timberlupus/borneo/assets/blc05mk3-sch.png

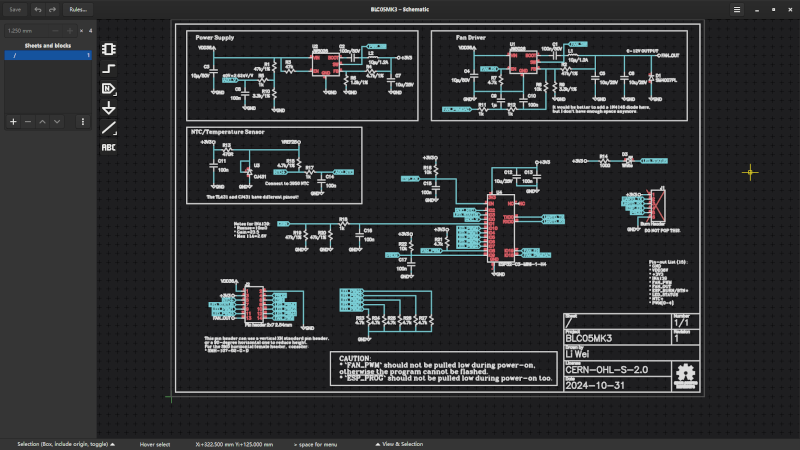
assets/blc05mk3-sch.png
