timberlupus/borneo/assets/blc06mk1-shot1.jpg

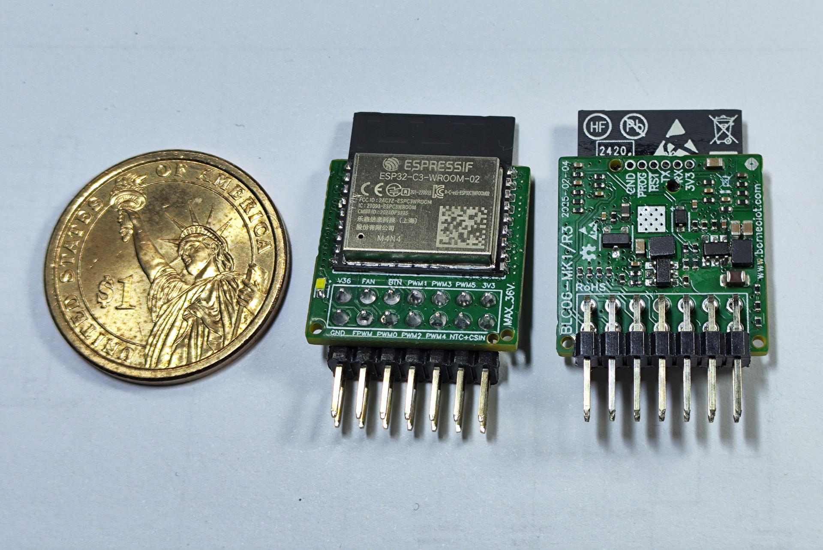
assets/blc06mk1-shot1.jpg
