timberlupus/borneo/hw/blb0657f/pool/3d_models/cache/6d752bc3-29b3-45df-8cf2-1e3aacefbcc6/3d_models/passive/resistor/R_0805_2012Metric.step

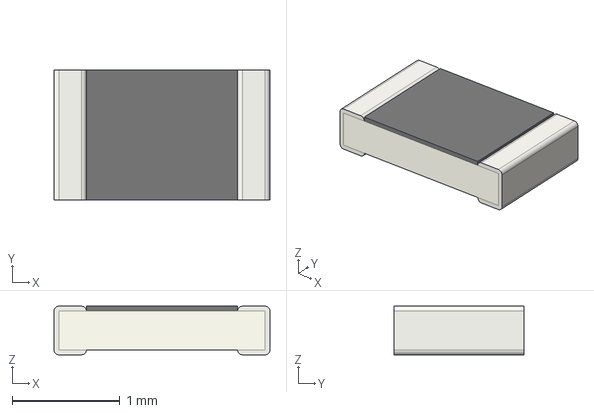
[picture p25: CAD file, 2025-01-13]
hw/blb0657f/pool/3d_models/cache/6d752bc3-29b3-45df-8cf2-1e3aacefbcc6/3d_models/passive/resistor/R_0805_2012Metric.step
2.00 x 1.20 x 0.45 mm
