timberlupus/borneo/hw/blb0657f/pool/3d_models/cache/8eeaf956-e4a0-4db5-95bb-b90e600e8069/3d_models/connector/b2w/2.54mm/2510_4p_smd_horizontal.step

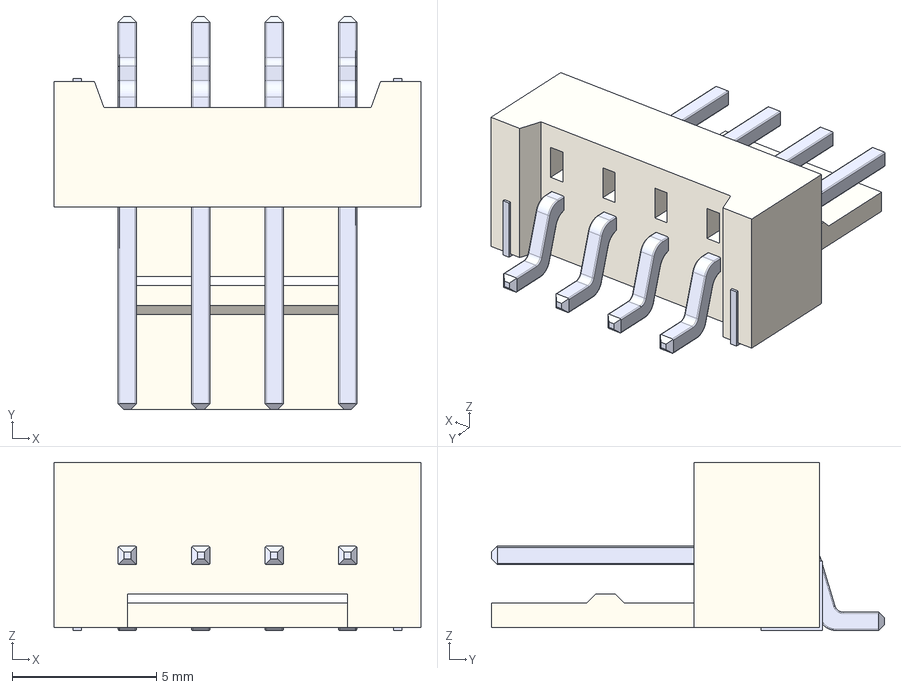
[picture p26: CAD file, 2025-01-13]
hw/blb0657f/pool/3d_models/cache/8eeaf956-e4a0-4db5-95bb-b90e600e8069/3d_models/connector/b2w/2.54mm/2510_4p_smd_horizontal.step
12.7 x 13.6 x 5.82 mm
