timberlupus/borneo/hw/blb0657f/pool/3d_models/cache/8eeaf956-e4a0-4db5-95bb-b90e600e8069/3d_models/connector/b2w/jst/2.00mm/S2B-PH-SM4-TB_LF__SN_.step

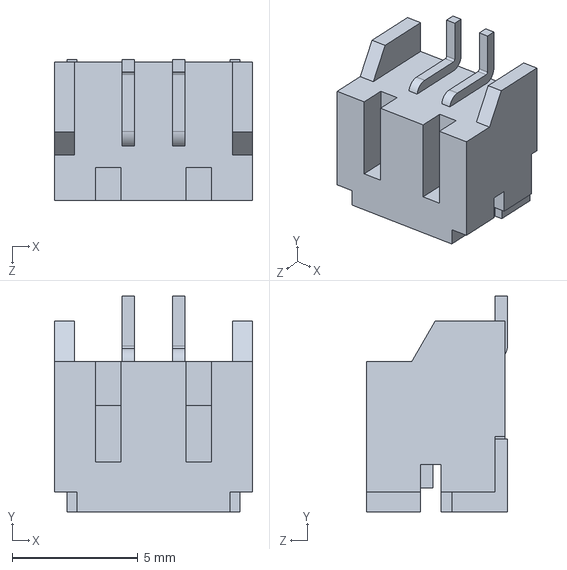
[picture p27: CAD file, 2025-02-11]
hw/blb0657f/pool/3d_models/cache/8eeaf956-e4a0-4db5-95bb-b90e600e8069/3d_models/connector/b2w/jst/2.00mm/S2B-PH-SM4-TB_LF__SN_.step
7.90 x 8.60 x 5.60 mm
