timberlupus/borneo/hw/blb0657f/pool/3d_models/cache/8eeaf956-e4a0-4db5-95bb-b90e600e8069/3d_models/connector/header/2.54mm/PinHeader_2x07_P2.54mm_Horizontal.step

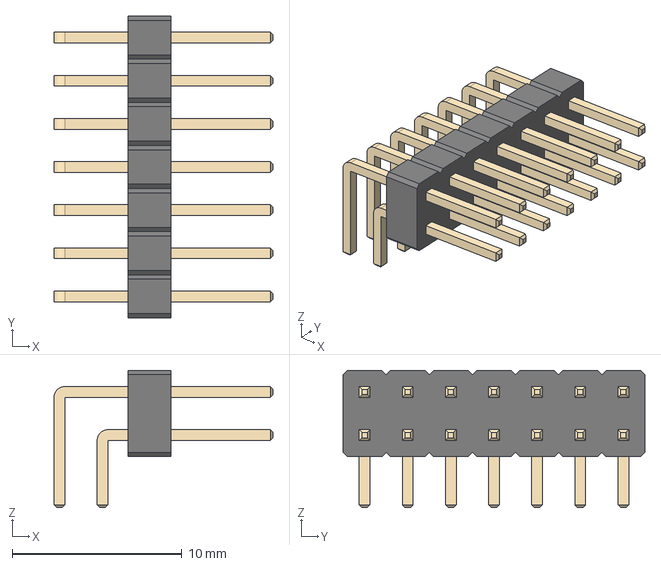
[picture p28: CAD file, 2025-01-13]
hw/blb0657f/pool/3d_models/cache/8eeaf956-e4a0-4db5-95bb-b90e600e8069/3d_models/connector/header/2.54mm/PinHeader_2x07_P2.54mm_Horizontal.step
12.9 x 17.8 x 8.08 mm
