timberlupus/borneo/hw/blb0657f/pool/3d_models/cache/8eeaf956-e4a0-4db5-95bb-b90e600e8069/3d_models/connector/header/samtec/2.54/SMH-107-02-G-D.stp

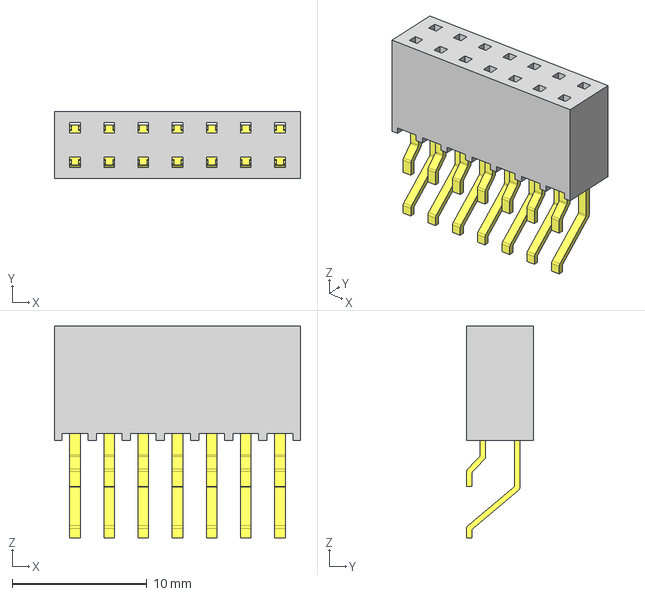
[picture p29: CAD file, 2025-01-13]
hw/blb0657f/pool/3d_models/cache/8eeaf956-e4a0-4db5-95bb-b90e600e8069/3d_models/connector/header/samtec/2.54/SMH-107-02-G-D.stp
18.3 x 4.95 x 15.7 mm
SMH-107-D_socket
C-08-03-07-D_SMH
