timberlupus/borneo/hw/blb0657f/pool/3d_models/cache/8eeaf956-e4a0-4db5-95bb-b90e600e8069/3d_models/connector/terminal-block/wago/2060-452_998-404.step

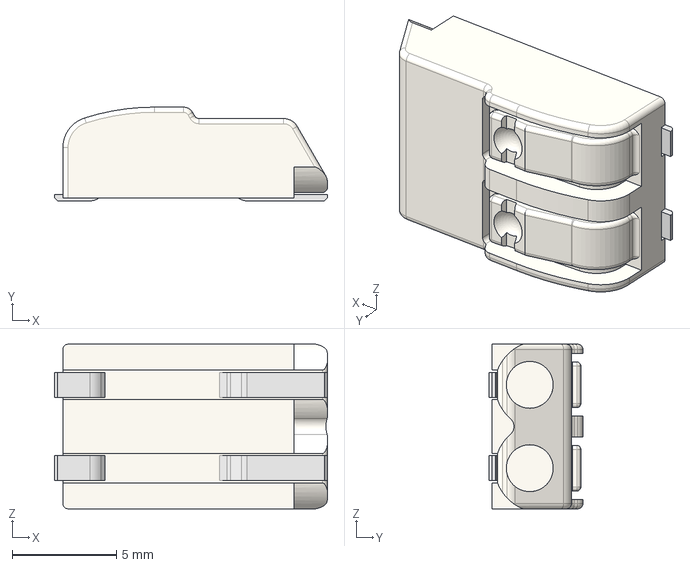
[picture p30: CAD file, 2025-02-11]
hw/blb0657f/pool/3d_models/cache/8eeaf956-e4a0-4db5-95bb-b90e600e8069/3d_models/connector/terminal-block/wago/2060-452_998-404.step
13.1 x 4.50 x 7.90 mm
