timberlupus/borneo/hw/blb0657f/pool/3d_models/cache/8eeaf956-e4a0-4db5-95bb-b90e600e8069/3d_models/ic/so/SOT-89-5.step

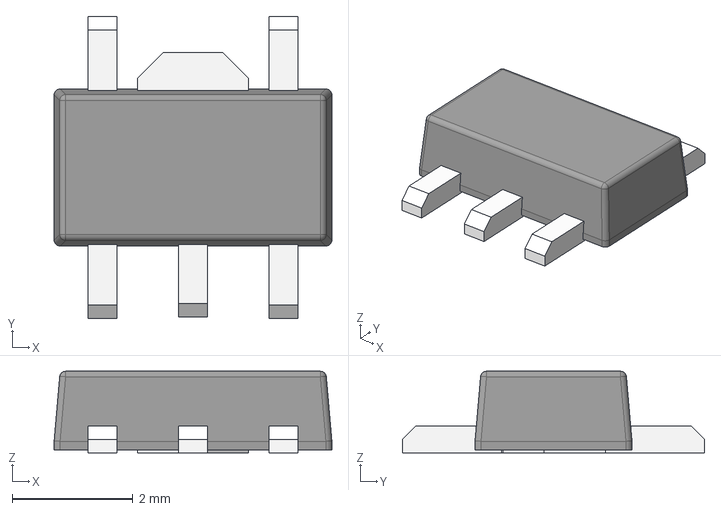
[picture p31: CAD file, 2025-02-04]
hw/blb0657f/pool/3d_models/cache/8eeaf956-e4a0-4db5-95bb-b90e600e8069/3d_models/ic/so/SOT-89-5.step
4.60 x 5.00 x 1.35 mm
