timberlupus/borneo/hw/blb0657f/pool/3d_models/cache/8eeaf956-e4a0-4db5-95bb-b90e600e8069/3d_models/module/bst/bld06-r1-3d-package.step

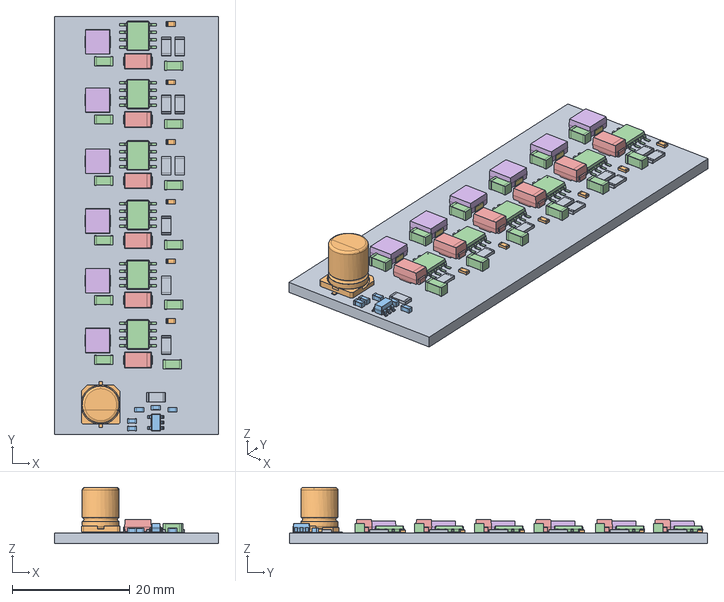
[picture p32: CAD file, 2025-02-08]
hw/blb0657f/pool/3d_models/cache/8eeaf956-e4a0-4db5-95bb-b90e600e8069/3d_models/module/bst/bld06-r1-3d-package.step
27.9 x 71.1 x 9.55 mm
