timberlupus/borneo/hw/blb0657f/pool/3d_models/cache/8eeaf956-e4a0-4db5-95bb-b90e600e8069/3d_models/opto/LED_SMDLED_1W_3W_R8-3DModel.step

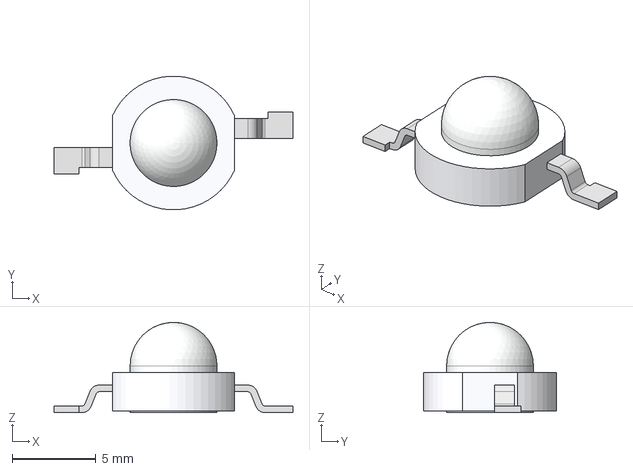
[picture p33: CAD file, 2025-01-13]
hw/blb0657f/pool/3d_models/cache/8eeaf956-e4a0-4db5-95bb-b90e600e8069/3d_models/opto/LED_SMDLED_1W_3W_R8-3DModel.step
14.3 x 7.99 x 5.40 mm
