timberlupus/borneo/hw/blb0657f/pool/3d_models/cache/8eeaf956-e4a0-4db5-95bb-b90e600e8069/3d_models/passive/capacitor/polarized/CP_Elec_6.3x7.7.step

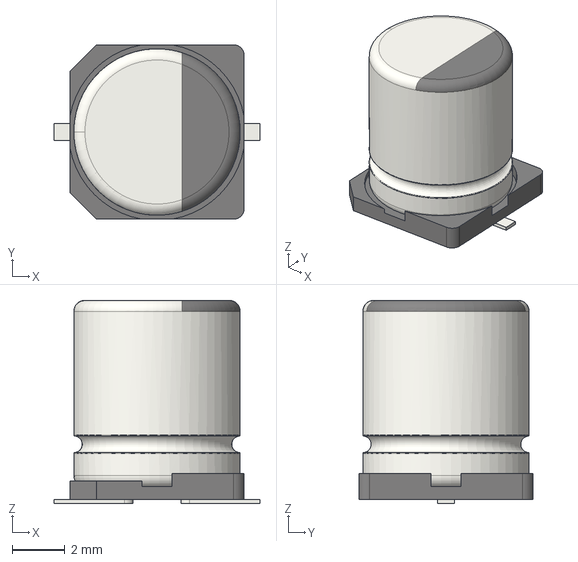
[picture p34: CAD file, 2025-01-13]
hw/blb0657f/pool/3d_models/cache/8eeaf956-e4a0-4db5-95bb-b90e600e8069/3d_models/passive/capacitor/polarized/CP_Elec_6.3x7.7.step
7.80 x 6.60 x 7.70 mm
