timberlupus/borneo/hw/blb0657f/pool/3d_models/cache/8eeaf956-e4a0-4db5-95bb-b90e600e8069/3d_models/passive/inductor/cjang/L_Changjiang_FNR4030S.step

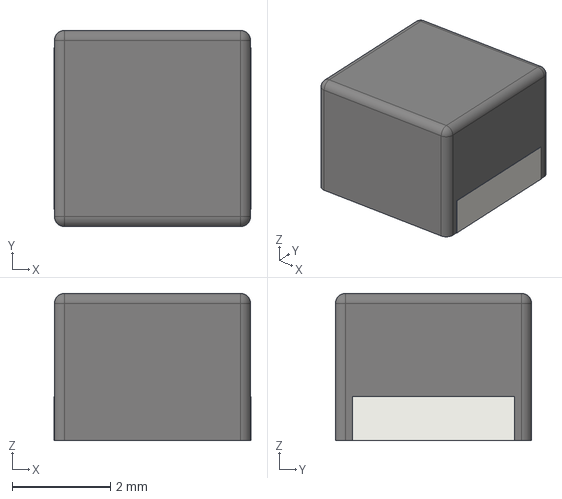
[picture p35: CAD file, 2025-02-04]
hw/blb0657f/pool/3d_models/cache/8eeaf956-e4a0-4db5-95bb-b90e600e8069/3d_models/passive/inductor/cjang/L_Changjiang_FNR4030S.step
4.02 x 4.00 x 3.00 mm
