timberlupus/borneo/hw/blb0657f/pool/3d_models/cache/8eeaf956-e4a0-4db5-95bb-b90e600e8069/3d_models/passive/inductor/tdk/L_TDK_SLF10145.step

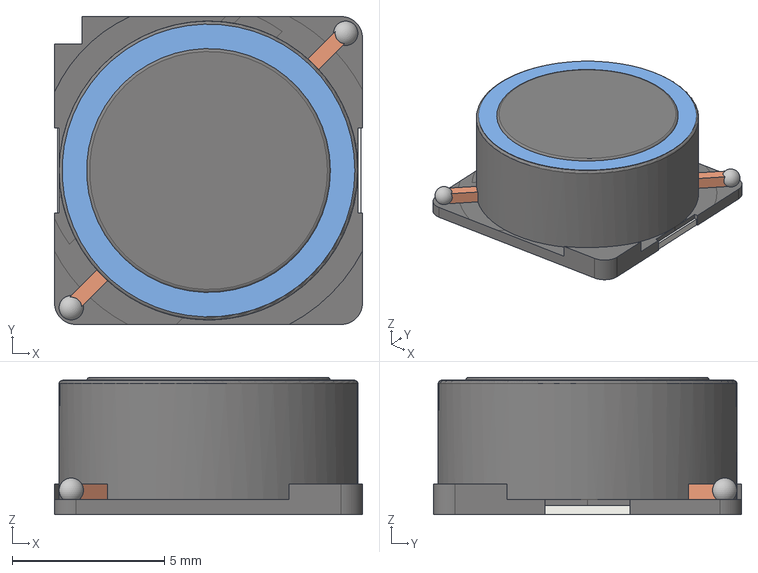
[picture p36: CAD file, 2025-01-13]
hw/blb0657f/pool/3d_models/cache/8eeaf956-e4a0-4db5-95bb-b90e600e8069/3d_models/passive/inductor/tdk/L_TDK_SLF10145.step
10.1 x 10.1 x 4.50 mm
