timberlupus/borneo/hw/blb0657f/pool/3d_models/cache/8eeaf956-e4a0-4db5-95bb-b90e600e8069/3d_models/passive/jump/smd/Jumper_0R0_10.2x1.5mm.step

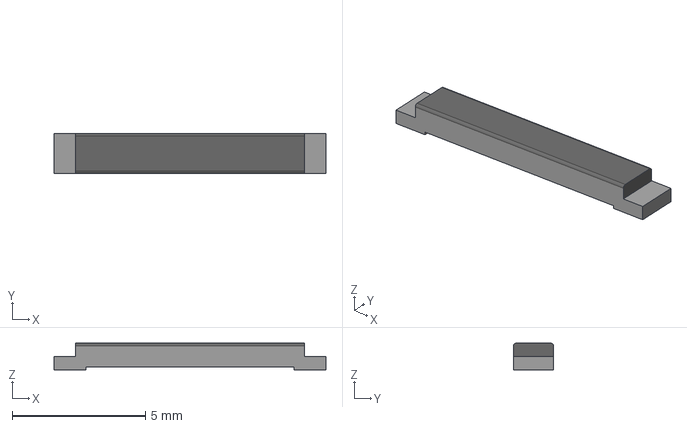
[picture p37: CAD file, 2025-02-08]
hw/blb0657f/pool/3d_models/cache/8eeaf956-e4a0-4db5-95bb-b90e600e8069/3d_models/passive/jump/smd/Jumper_0R0_10.2x1.5mm.step
10.2 x 1.50 x 1.00 mm
