timberlupus/borneo/hw/blb08103/pool/3d_models/cache/8eeaf956-e4a0-4db5-95bb-b90e600e8069/3d_models/connector/b2w/jst/2.50mm/S4B-XH-SM4-TB.STEP

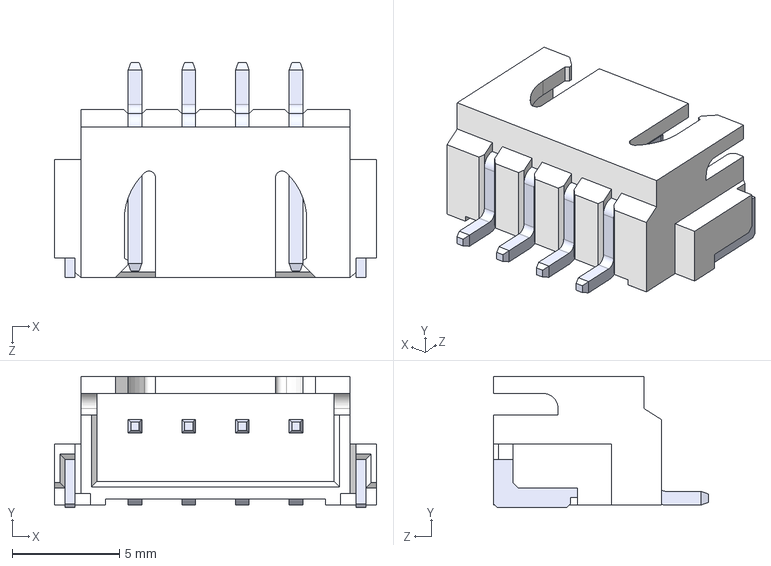
[picture p38: CAD file, 2025-01-13]
hw/blb08103/pool/3d_models/cache/8eeaf956-e4a0-4db5-95bb-b90e600e8069/3d_models/connector/b2w/jst/2.50mm/S4B-XH-SM4-TB.STEP
15.0 x 6.12 x 10.0 mm
SxB-XH-SM4-TB_4
pin^SxB-XH-SM4-TB Ass x 4
