timberlupus/borneo/hw/blb08103/pool/3d_models/cache/8eeaf956-e4a0-4db5-95bb-b90e600e8069/3d_models/ic/so/TSSOP-20_4.4x6.5mm_P0.65mm.step

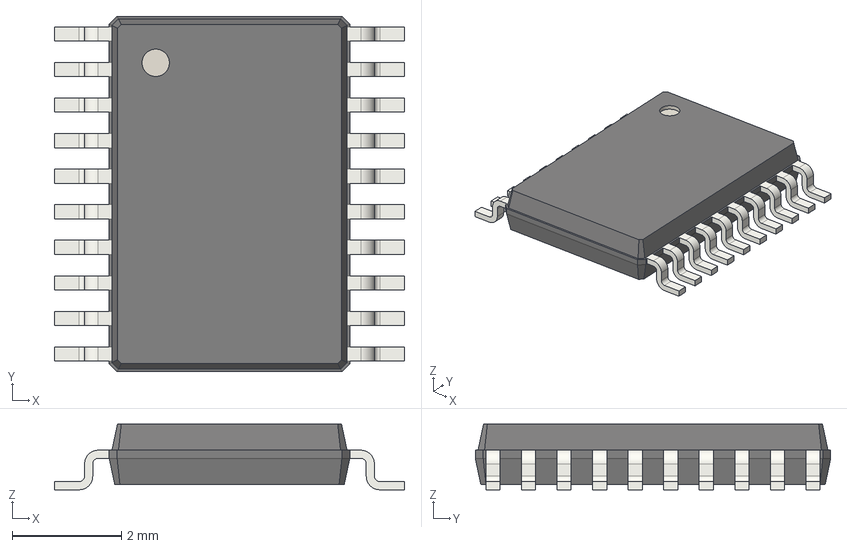
[picture p39: CAD file, 2025-01-13]
hw/blb08103/pool/3d_models/cache/8eeaf956-e4a0-4db5-95bb-b90e600e8069/3d_models/ic/so/TSSOP-20_4.4x6.5mm_P0.65mm.step
6.40 x 6.50 x 1.20 mm
