timberlupus/borneo/hw/blb08103/pool/3d_models/cache/8eeaf956-e4a0-4db5-95bb-b90e600e8069/3d_models/passive/fuse/Fuse_1210_3225Metric.step

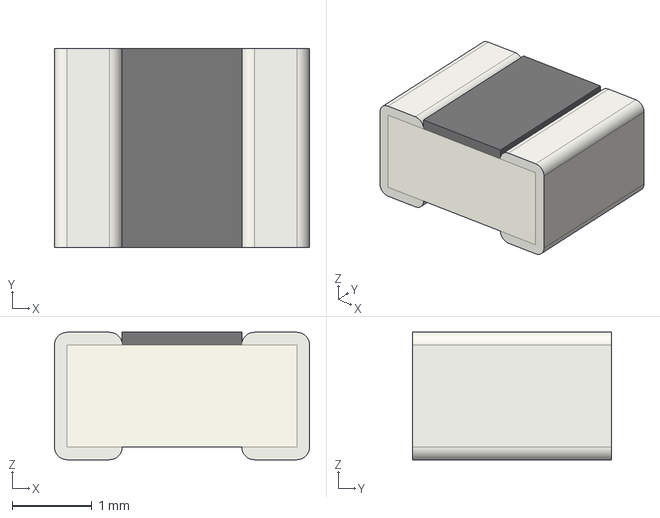
[picture p40: CAD file, 2025-01-13]
hw/blb08103/pool/3d_models/cache/8eeaf956-e4a0-4db5-95bb-b90e600e8069/3d_models/passive/fuse/Fuse_1210_3225Metric.step
3.20 x 2.50 x 1.60 mm
