timberlupus/borneo/hw/blc06/pool/3d_models/cache/6d752bc3-29b3-45df-8cf2-1e3aacefbcc6/3d_models/connector/header/2.54mm/PinHeader_2x08_P2.54mm_Vertical.step

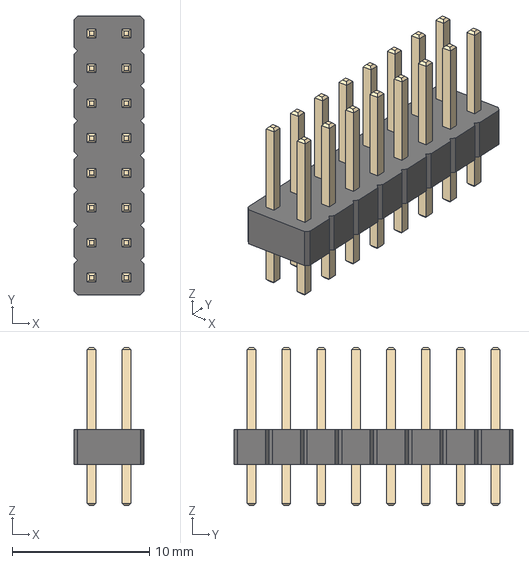
[picture p41: CAD file, 2025-02-01]
hw/blc06/pool/3d_models/cache/6d752bc3-29b3-45df-8cf2-1e3aacefbcc6/3d_models/connector/header/2.54mm/PinHeader_2x08_P2.54mm_Vertical.step
5.08 x 20.3 x 11.5 mm
