timberlupus/borneo/hw/blc06/pool/3d_models/cache/6d752bc3-29b3-45df-8cf2-1e3aacefbcc6/3d_models/diode/D_SOD-323.step

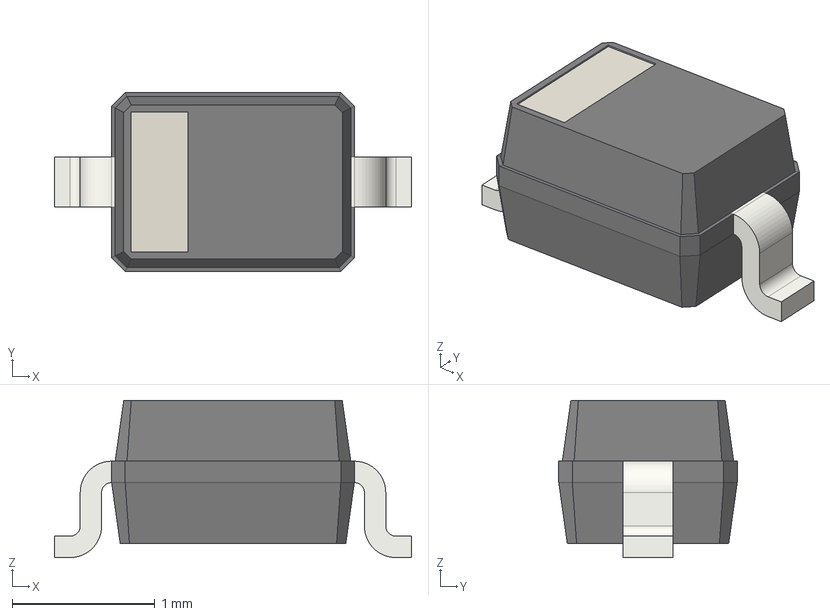
[picture p42: CAD file, 2025-01-13]
hw/blc06/pool/3d_models/cache/6d752bc3-29b3-45df-8cf2-1e3aacefbcc6/3d_models/diode/D_SOD-323.step
2.50 x 1.25 x 1.10 mm
