timberlupus/borneo/hw/blc06/pool/3d_models/cache/6d752bc3-29b3-45df-8cf2-1e3aacefbcc6/3d_models/passive/resistor/R_0402_1005Metric.step

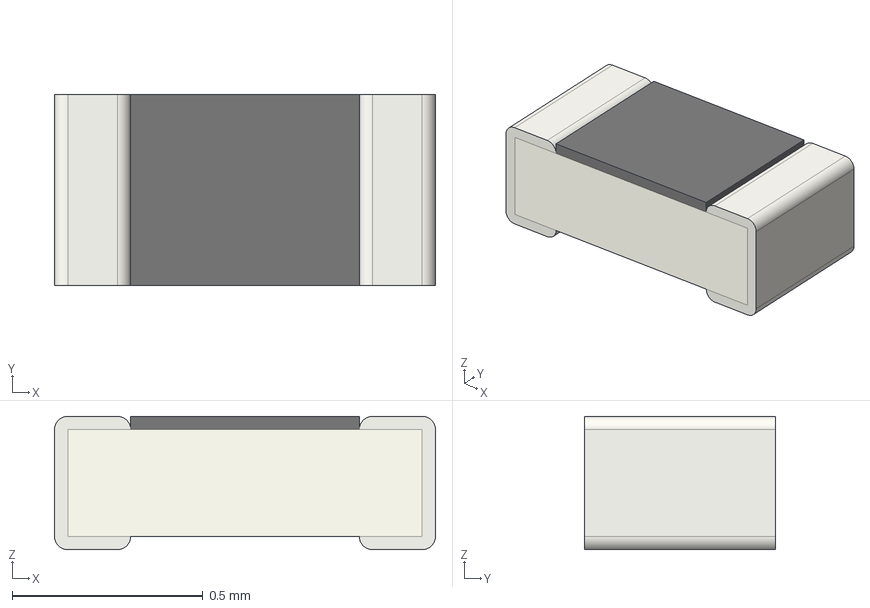
[picture p45: CAD file, 2025-01-13]
hw/blc06/pool/3d_models/cache/6d752bc3-29b3-45df-8cf2-1e3aacefbcc6/3d_models/passive/resistor/R_0402_1005Metric.step
1.00 x 0.5 x 0.35 mm
