timberlupus/borneo/hw/blc06/pool/3d_models/cache/8eeaf956-e4a0-4db5-95bb-b90e600e8069/3d_models/connector/header/1.27mm/PinHeader_1x06_P1.27mm_Vertical.step

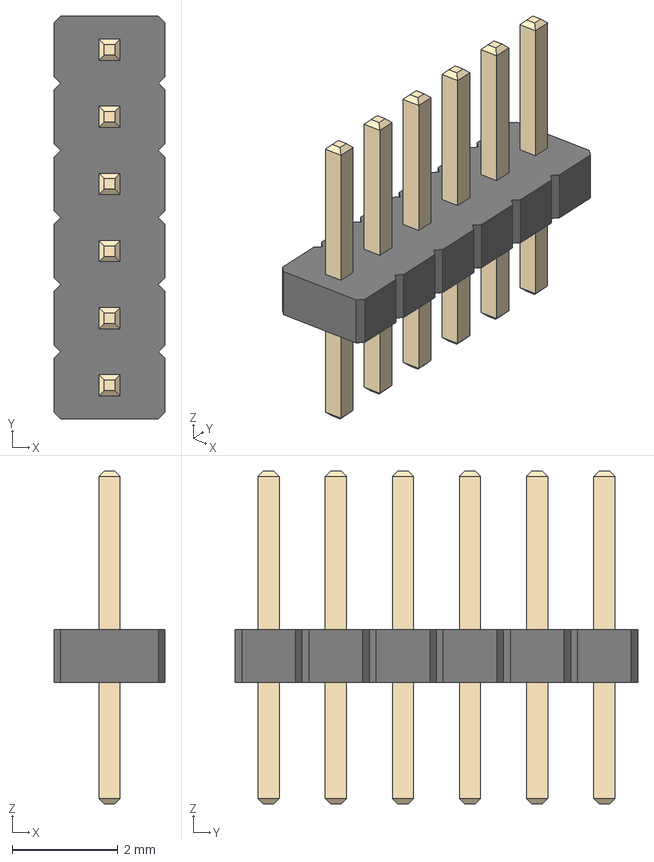
[picture p46: CAD file, 2025-01-13]
hw/blc06/pool/3d_models/cache/8eeaf956-e4a0-4db5-95bb-b90e600e8069/3d_models/connector/header/1.27mm/PinHeader_1x06_P1.27mm_Vertical.step
2.10 x 7.62 x 6.30 mm
