timberlupus/borneo/hw/blc06/pool/3d_models/cache/8eeaf956-e4a0-4db5-95bb-b90e600e8069/3d_models/ic/qfn/QFN-28-1EP_4x4mm_P0.4mm_EP2.4x2.4mm.step

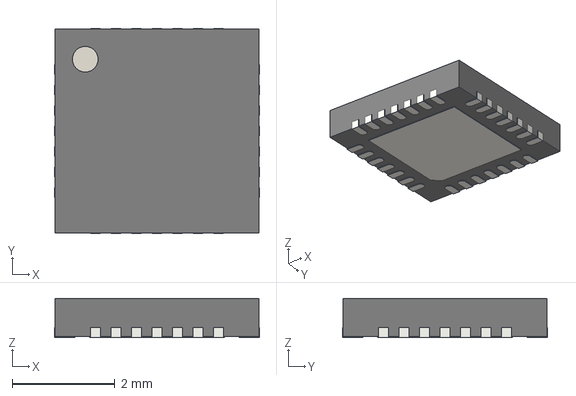
[picture p47: CAD file, 2025-01-13]
hw/blc06/pool/3d_models/cache/8eeaf956-e4a0-4db5-95bb-b90e600e8069/3d_models/ic/qfn/QFN-28-1EP_4x4mm_P0.4mm_EP2.4x2.4mm.step
4.00 x 4.00 x 0.77 mm
