timberlupus/borneo/hw/blc06/pool/3d_models/cache/8eeaf956-e4a0-4db5-95bb-b90e600e8069/3d_models/ic/so/SOT-23-6.step

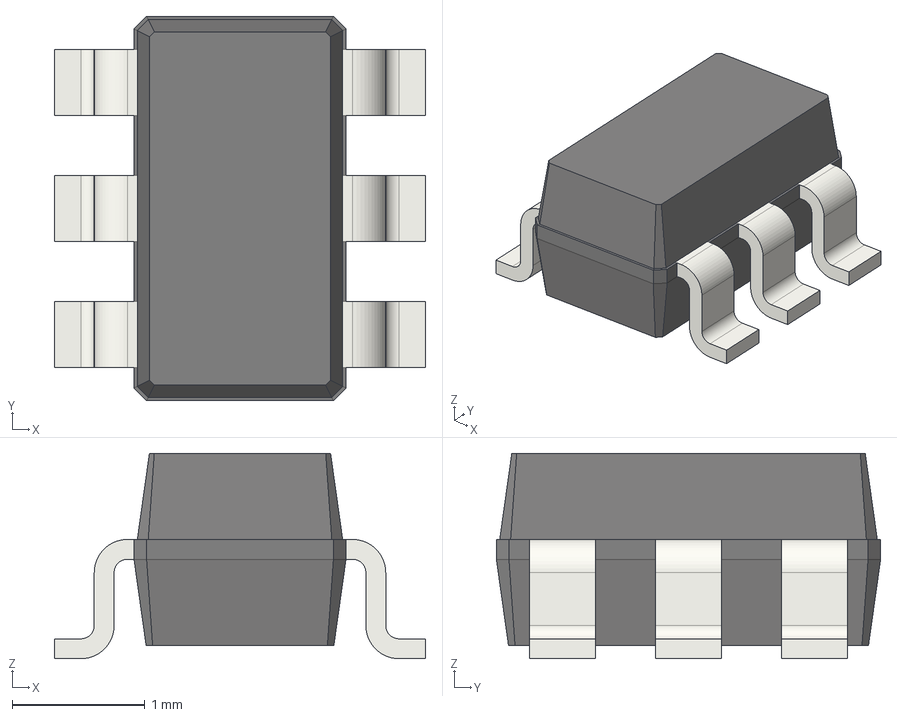
[picture p48: CAD file, 2025-01-13]
hw/blc06/pool/3d_models/cache/8eeaf956-e4a0-4db5-95bb-b90e600e8069/3d_models/ic/so/SOT-23-6.step
2.80 x 2.90 x 1.55 mm
