timberlupus/borneo/hw/blc06/pool/3d_models/cache/8eeaf956-e4a0-4db5-95bb-b90e600e8069/3d_models/ic/wson/WSON-8-1EP_2x2mm_P0.5mm_EP0.9x1.6mm.step

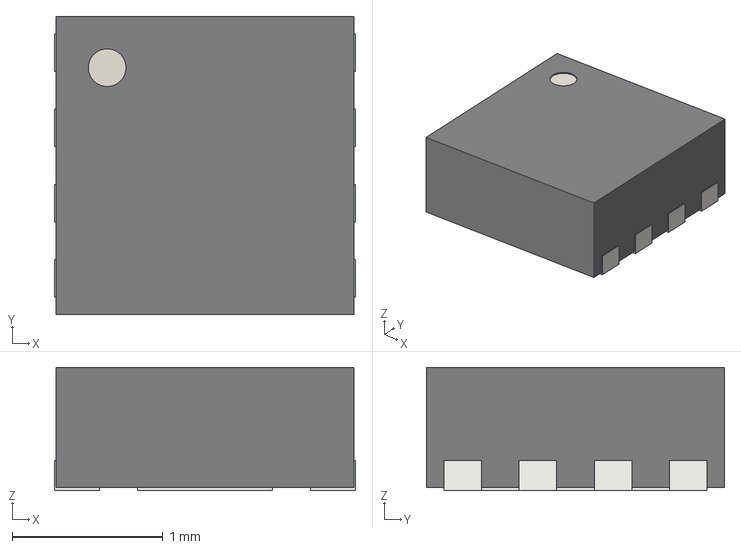
[picture p49: CAD file, 2025-02-01]
hw/blc06/pool/3d_models/cache/8eeaf956-e4a0-4db5-95bb-b90e600e8069/3d_models/ic/wson/WSON-8-1EP_2x2mm_P0.5mm_EP0.9x1.6mm.step
2.00 x 1.98 x 0.82 mm
