timberlupus/borneo/hw/blc06/pool/3d_models/cache/8eeaf956-e4a0-4db5-95bb-b90e600e8069/3d_models/module/rf/espressif/ESP32-C3-WROOM-02.stp

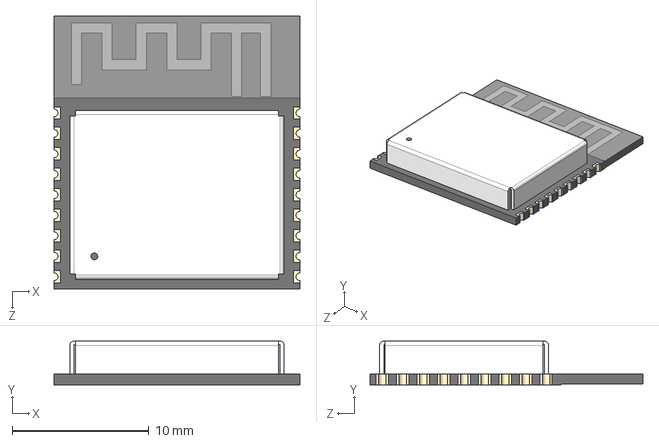
[picture p50: CAD file, 2025-03-12]
hw/blc06/pool/3d_models/cache/8eeaf956-e4a0-4db5-95bb-b90e600e8069/3d_models/module/rf/espressif/ESP32-C3-WROOM-02.stp
18.0 x 3.20 x 20.0 mm
