timberlupus/borneo/hw/blc06/pool/3d_models/cache/8eeaf956-e4a0-4db5-95bb-b90e600e8069/3d_models/opto/LED_0402_1005Metric.step

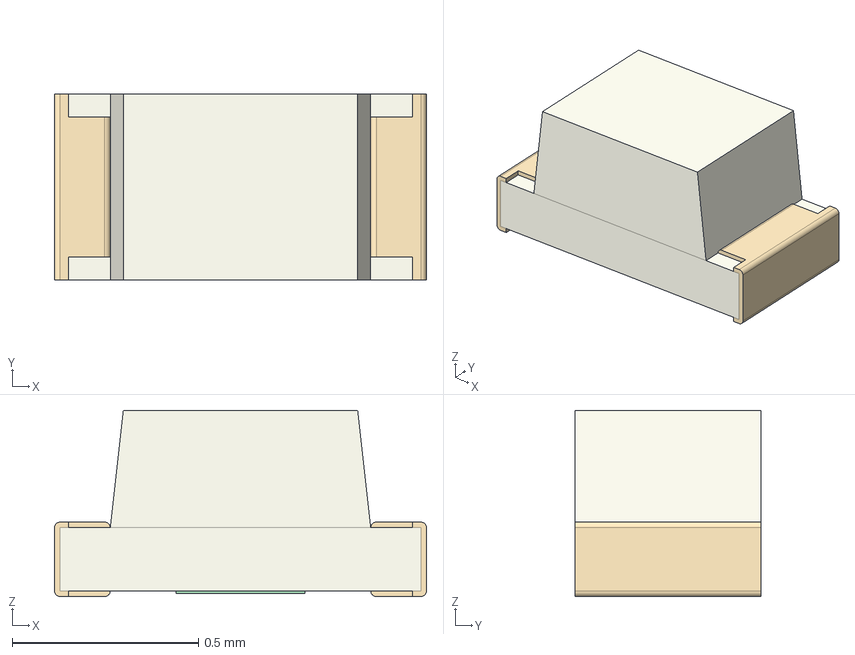
[picture p51: CAD file, 2025-02-17]
hw/blc06/pool/3d_models/cache/8eeaf956-e4a0-4db5-95bb-b90e600e8069/3d_models/opto/LED_0402_1005Metric.step
1.00 x 0.5 x 0.5 mm
