timberlupus/borneo/hw/blc06/pool/3d_models/cache/8eeaf956-e4a0-4db5-95bb-b90e600e8069/3d_models/passive/inductor/cjang/L_Changjiang_FNR3015S.step

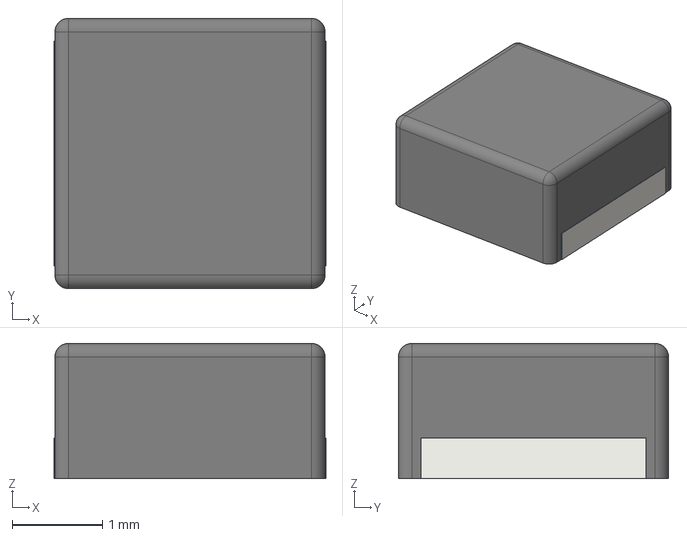
[picture p53: CAD file, 2025-01-13]
hw/blc06/pool/3d_models/cache/8eeaf956-e4a0-4db5-95bb-b90e600e8069/3d_models/passive/inductor/cjang/L_Changjiang_FNR3015S.step
3.02 x 3.00 x 1.50 mm
