timberlupus/borneo/hw/bld6f/pool/3d_models/cache/6d752bc3-29b3-45df-8cf2-1e3aacefbcc6/3d_models/passive/resistor/R_0603_1608Metric.step

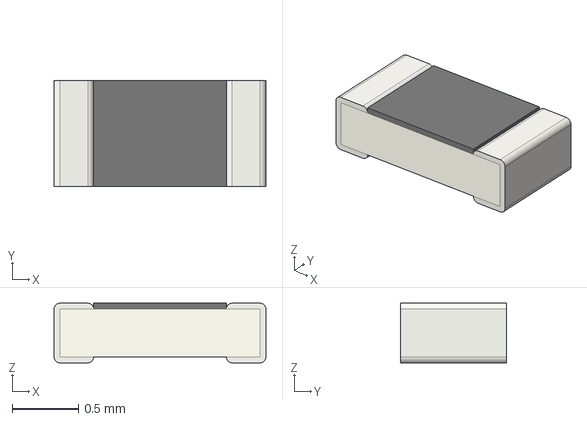
[picture p54: CAD file, 2025-01-13]
hw/bld6f/pool/3d_models/cache/6d752bc3-29b3-45df-8cf2-1e3aacefbcc6/3d_models/passive/resistor/R_0603_1608Metric.step
1.60 x 0.8 x 0.45 mm
