timberlupus/borneo/hw/bld6f/pool/3d_models/cache/8eeaf956-e4a0-4db5-95bb-b90e600e8069/3d_models/passive/inductor/sunlord/MWSA0402S.step

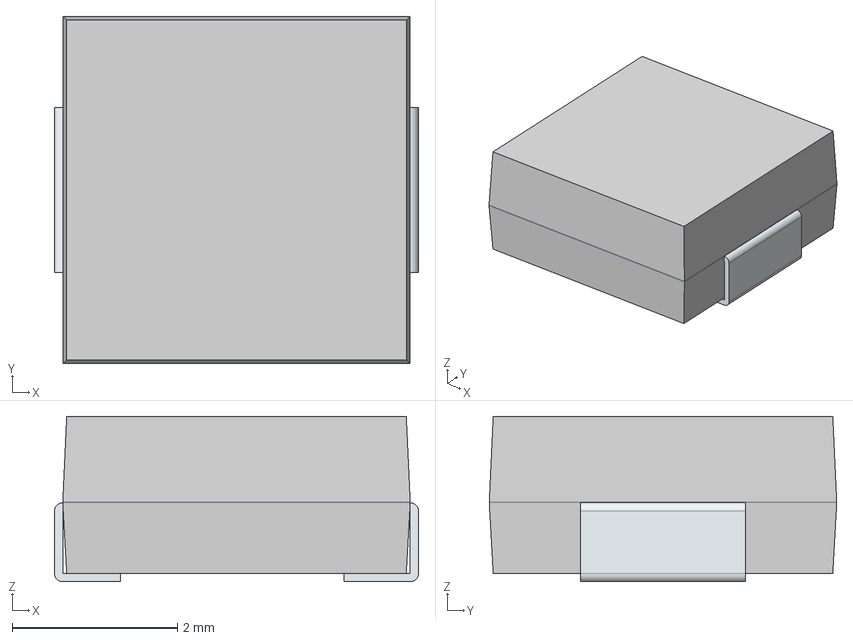
[picture p55: CAD file, 2025-02-08]
hw/bld6f/pool/3d_models/cache/8eeaf956-e4a0-4db5-95bb-b90e600e8069/3d_models/passive/inductor/sunlord/MWSA0402S.step
4.40 x 4.20 x 2.00 mm
FilletPin1
FilletPin2
