timberlupus/borneo/hw/bdb6mk1/pool/3d_models/cache/6d752bc3-29b3-45df-8cf2-1e3aacefbcc6/3d_models/ic/so/SOT-23.step

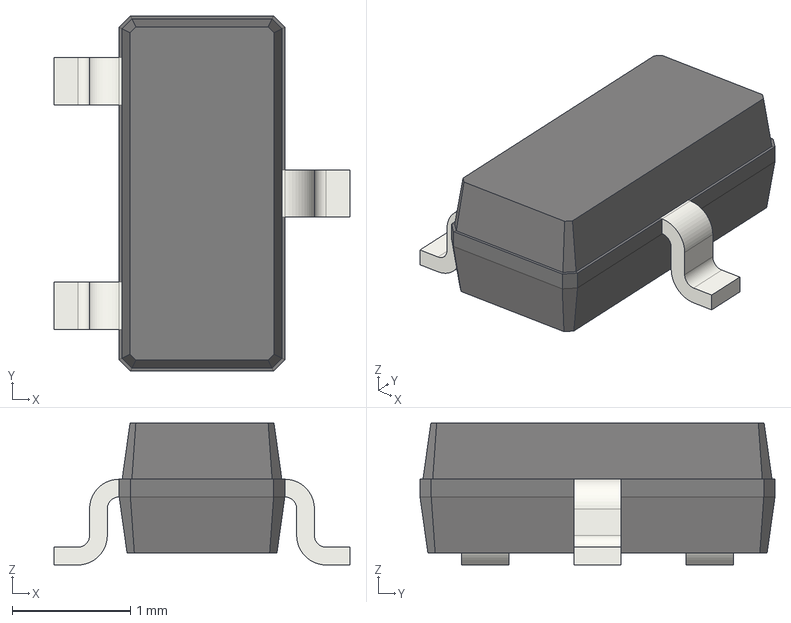
[picture p56: CAD file, 2025-01-13]
hw/bdb6mk1/pool/3d_models/cache/6d752bc3-29b3-45df-8cf2-1e3aacefbcc6/3d_models/ic/so/SOT-23.step
2.50 x 3.00 x 1.20 mm
