timberlupus/borneo/hw/bdb6mk1/pool/3d_models/cache/8eeaf956-e4a0-4db5-95bb-b90e600e8069/3d_models/module/rf/espressif/ESP32-C3-WROOM-02.STEP

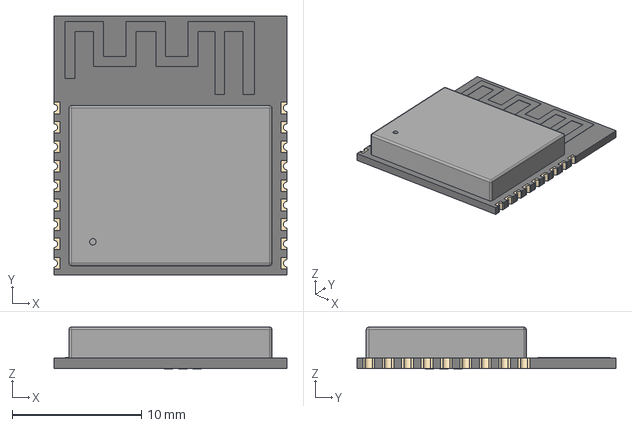
[picture p57: CAD file, 2025-02-01]
hw/bdb6mk1/pool/3d_models/cache/8eeaf956-e4a0-4db5-95bb-b90e600e8069/3d_models/module/rf/espressif/ESP32-C3-WROOM-02.STEP
18.0 x 20.0 x 3.24 mm
