timberlupus/borneo/hw/blb0657f/pool/3d_models/cache/8eeaf956-e4a0-4db5-95bb-b90e600e8069/3d_models/ic/so/SSOP-8_3.9x5.05mm_P1.27mm.step

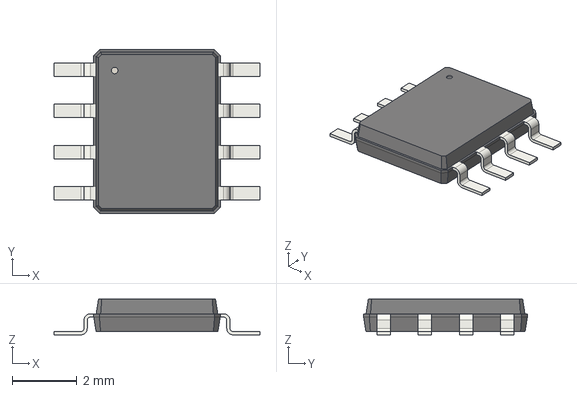
[picture p59: CAD file, 2025-02-04]
hw/blb0657f/pool/3d_models/cache/8eeaf956-e4a0-4db5-95bb-b90e600e8069/3d_models/ic/so/SSOP-8_3.9x5.05mm_P1.27mm.step
6.35 x 5.05 x 1.10 mm
