timberlupus/borneo/hw/blb0657f/pool/3d_models/cache/8eeaf956-e4a0-4db5-95bb-b90e600e8069/3d_models/opto/LED_SMDLED_RGB_3W-3DModel.step

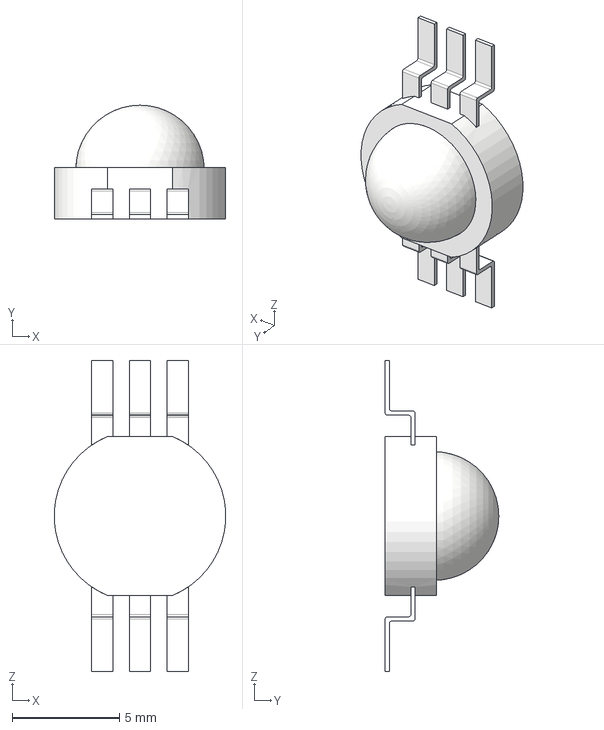
[picture p60: CAD file, 2025-01-13]
hw/blb0657f/pool/3d_models/cache/8eeaf956-e4a0-4db5-95bb-b90e600e8069/3d_models/opto/LED_SMDLED_RGB_3W-3DModel.step
7.98 x 5.30 x 14.5 mm
3w power led_1
3w power led lens
