timberlupus/borneo/hw/blb0657f/pool/3d_models/cache/8eeaf956-e4a0-4db5-95bb-b90e600e8069/3d_models/passive/jump/smd/Jump_0R0_8.2x1.5-Part.step

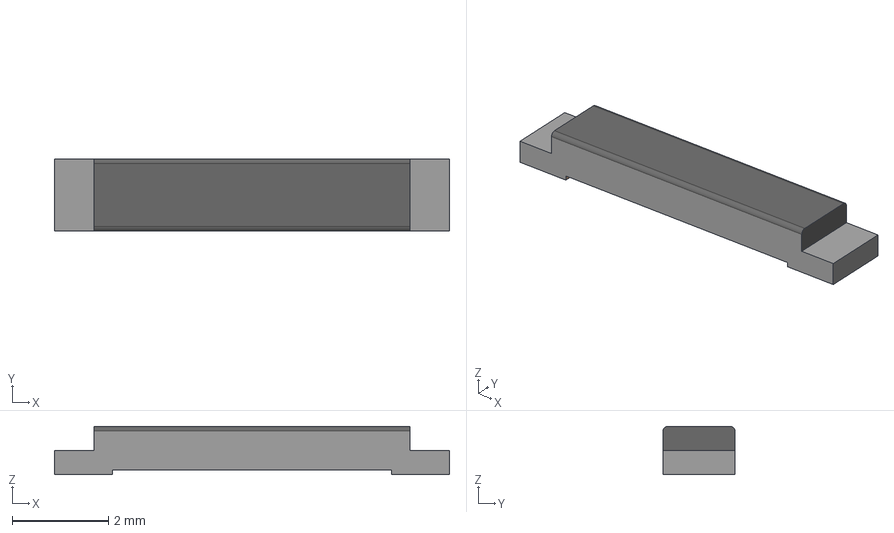
[picture p61: CAD file, 2025-01-13]
hw/blb0657f/pool/3d_models/cache/8eeaf956-e4a0-4db5-95bb-b90e600e8069/3d_models/passive/jump/smd/Jump_0R0_8.2x1.5-Part.step
8.20 x 1.50 x 1.00 mm
