timberlupus/borneo/hw/blc06/pool/3d_models/cache/6d752bc3-29b3-45df-8cf2-1e3aacefbcc6/3d_models/connector/header/2.54mm/PinHeader_2x07_P2.54mm_Vertical.step

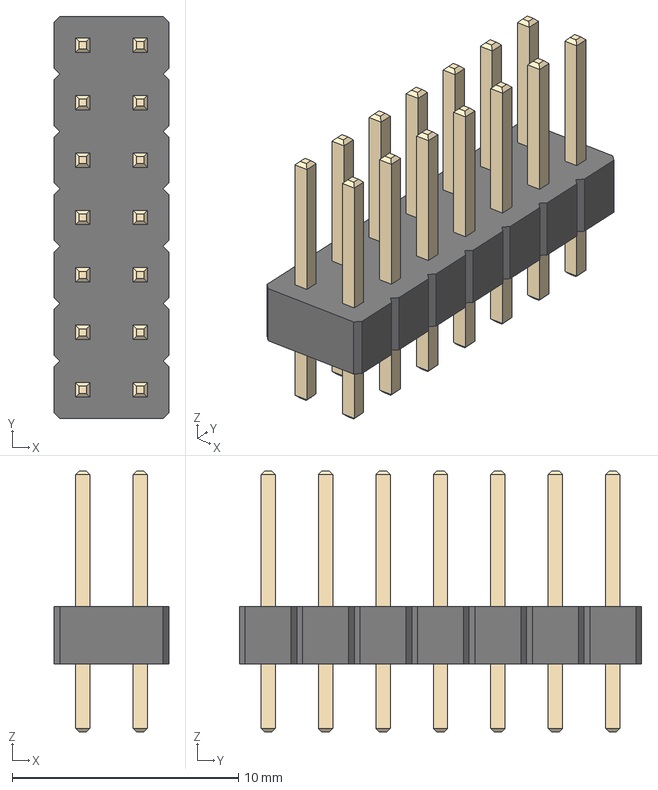
[picture p62: CAD file, 2025-01-13]
hw/blc06/pool/3d_models/cache/6d752bc3-29b3-45df-8cf2-1e3aacefbcc6/3d_models/connector/header/2.54mm/PinHeader_2x07_P2.54mm_Vertical.step
5.08 x 17.8 x 11.5 mm
