timberlupus/borneo/hw/blc06/pool/3d_models/cache/8eeaf956-e4a0-4db5-95bb-b90e600e8069/3d_models/module/rf/espressif/ESP32-C3-MINI-1.STEP

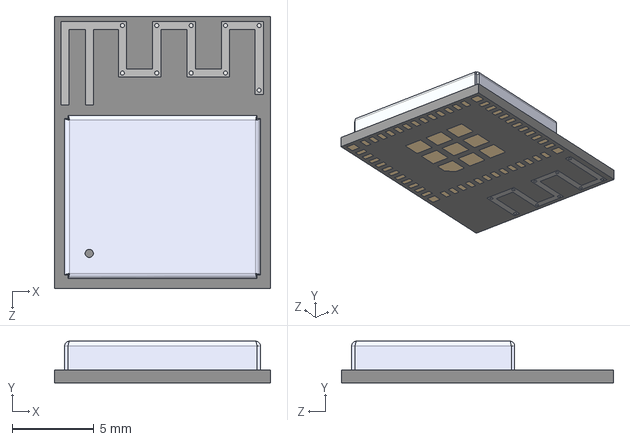
[picture p64: CAD file, 2025-01-13]
hw/blc06/pool/3d_models/cache/8eeaf956-e4a0-4db5-95bb-b90e600e8069/3d_models/module/rf/espressif/ESP32-C3-MINI-1.STEP
13.2 x 2.55 x 16.6 mm
