timberlupus/borneo/hw/blc06/pool/3d_models/cache/8eeaf956-e4a0-4db5-95bb-b90e600e8069/3d_models/passive/inductor/L_1008_2520Metric.step

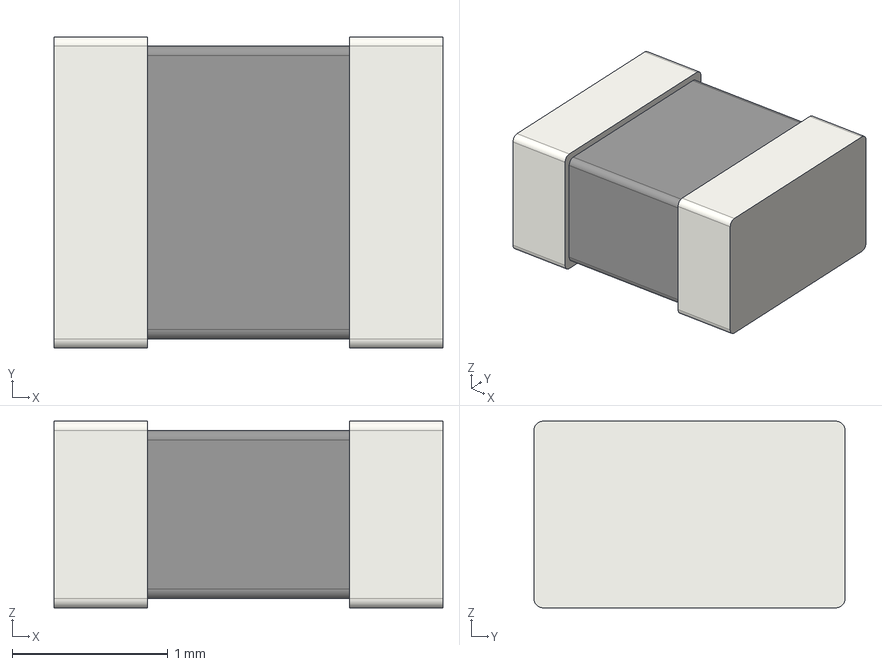
[picture p65: CAD file, 2025-01-13]
hw/blc06/pool/3d_models/cache/8eeaf956-e4a0-4db5-95bb-b90e600e8069/3d_models/passive/inductor/L_1008_2520Metric.step
2.50 x 2.00 x 1.20 mm
