timberlupus/borneo/fw/lyfi/main/src/led/correction-lut.c

#include <stdlib.h>
#include <stdbool.h>
#include <time.h>

#include <freertos/FreeRTOS.h>
#include <freertos/semphr.h>

#include "led.h"

// CIE 1931 brightness curve lookup table (perceptual uniform)
const led_duty_t LED_CORLUT_CIE1931[] = {
    0,    0,    0,    0,    0,    1,    1,    1,    1,    1,    1,    1,    1,    1,    2,    2,    2,    2,    2,
    2,    2,    2,    2,    3,    3,    3,    3,    3,    3,    3,    3,    3,    4,    4,    4,    4,    4,    4,
    4,    4,    4,    5,    5,    5,    5,    5,    5,    5,    5,    5,    6,    6,    6,    6,    6,    6,    6,
    6,    6,    7,    7,    7,    7,    7,    7,    7,    7,    7,    8,    8,    8,    8,    8,    8,    8,    8,
    8,    9,    9,    9,    9,    9,    9,    9,    9,    9,    10,   10,   10,   10,   10,   10,   10,   10,   10,
    11,   11,   11,   11,   11,   11,   11,   11,   11,   12,   12,   12,   12,   12,   12,   12,   12,   12,   13,
    13,   13,   13,   13,   13,   13,   13,   13,   14,   14,   14,   14,   14,   14,   14,   14,   14,   15,   15,
    15,   15,   15,   15,   15,   15,   15,   15,   16,   16,   16,   16,   16,   16,   16,   16,   16,   17,   17,
    17,   17,   17,   17,   17,   17,   17,   18,   18,   18,   18,   18,   18,   18,   18,   18,   19,   19,   19,
    19,   19,   19,   19,   19,   19,   20,   20,   20,   20,   20,   20,   20,   20,   20,   21,   21,   21,   21,
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
    90,   90,   91,   91,   91,   91,   92,   92,   92,   92,   93,   93,   93,   94,   94,   94,   94,   95,   95,
    95,   96,   96,   96,   96,   97,   97,   97,   98,   98,   98,   98,   99,   99,   99,   100,  100,  100,  100,
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
};
